jackshafer/zmk-config-biba40/images/Biba40_v2_underside.jpg

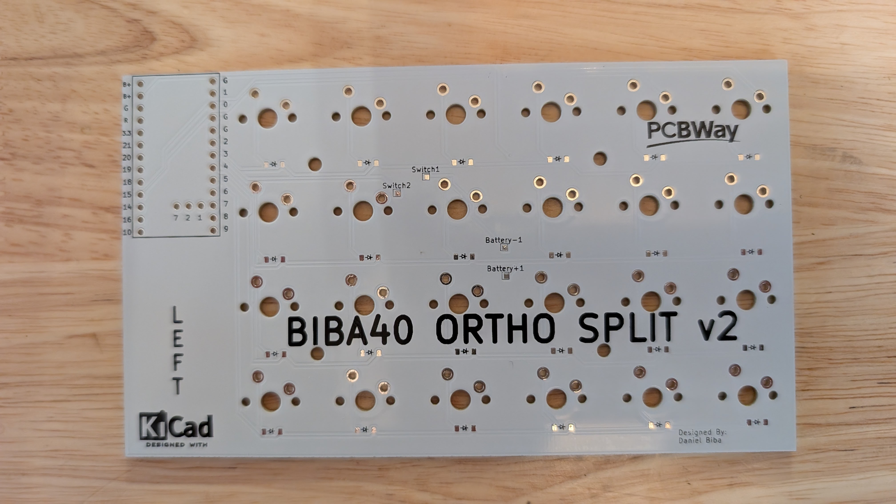
images/Biba40_v2_underside.jpg
