jackshafer/zmk-config-biba40/images/grey_and_purple_keycaps.jpg

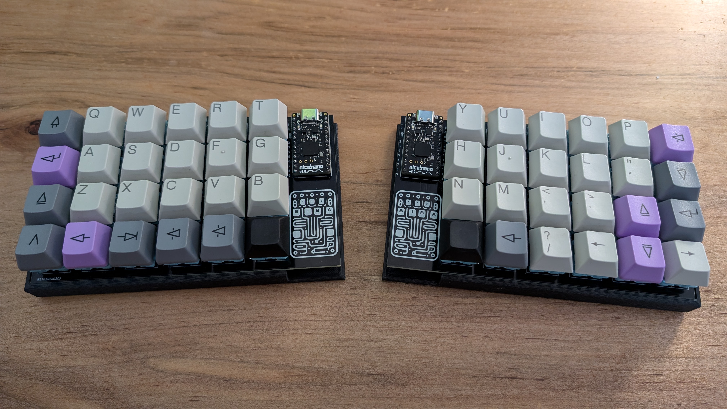
images/grey_and_purple_keycaps.jpg
