jackshafer/zmk-config-biba40/images/nice_nano.jpg

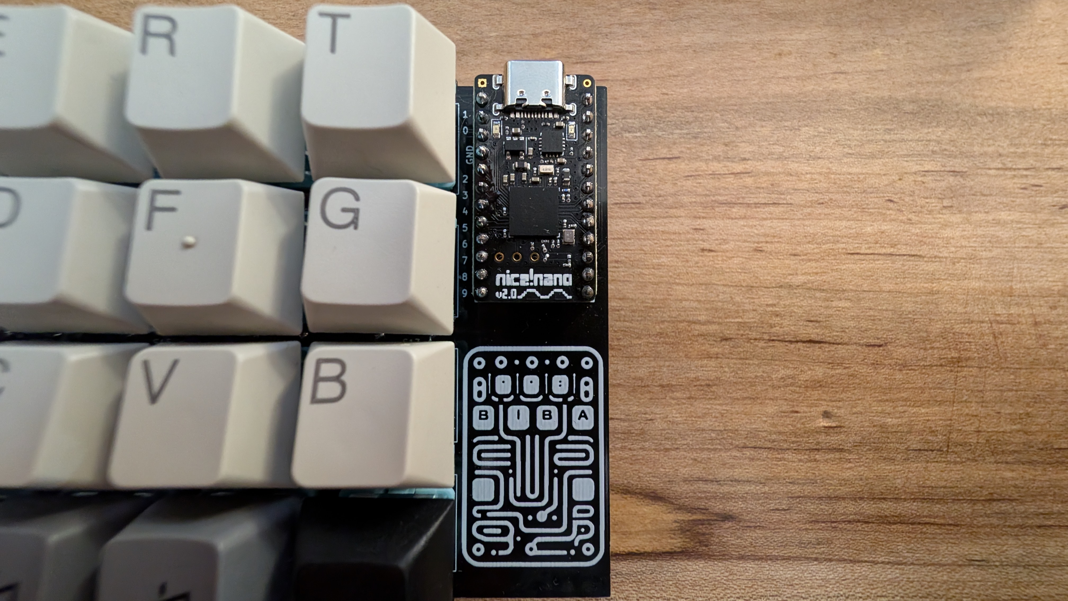
images/nice_nano.jpg
