jackshafer/zmk-config-biba40/images/power_switch.jpg

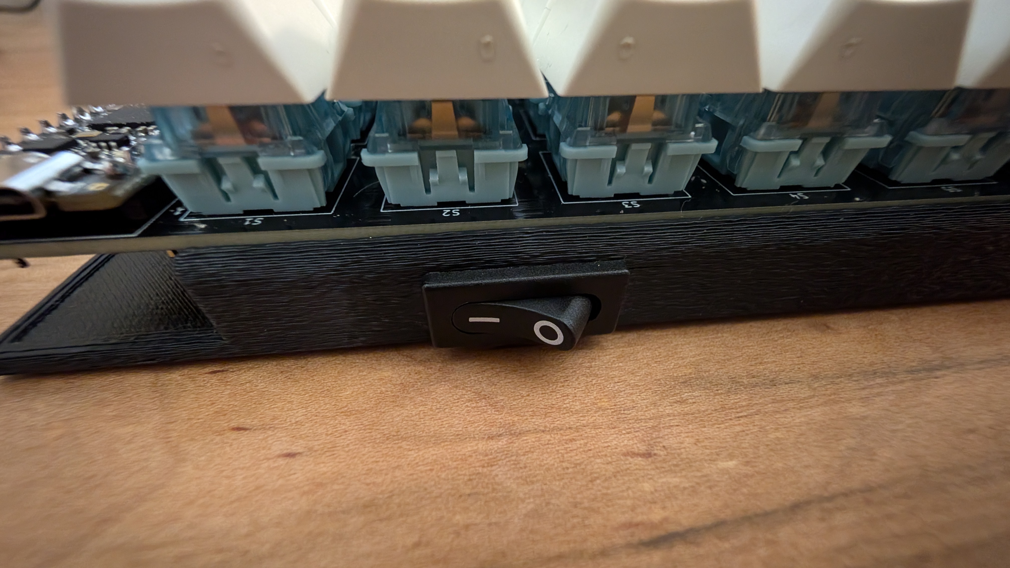
images/power_switch.jpg
