jackshafer/zmk-config-biba40/images/PXL_20250227_141126423.jpg

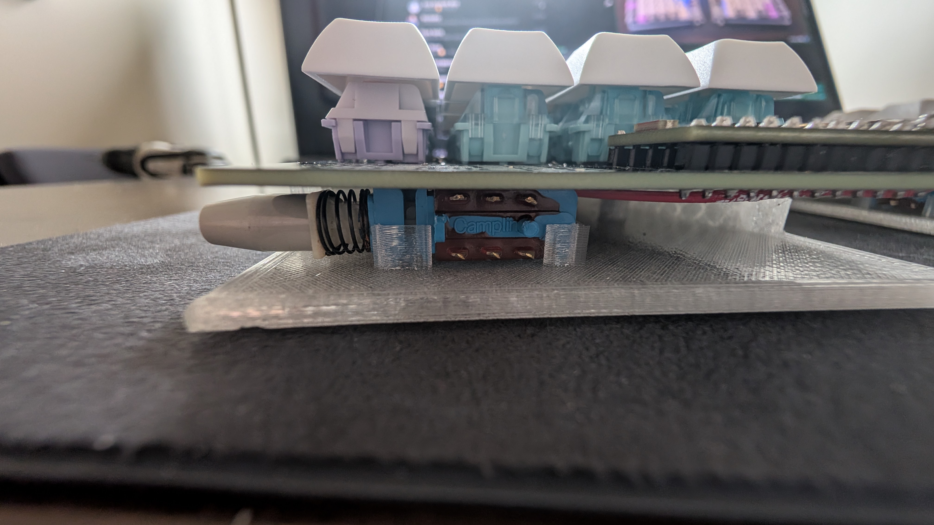
images/PXL_20250227_141126423.jpg
