jackshafer/zmk-config-biba40/images/PXL_20250227_221245341.PORTRAIT.ORIGINAL.jpg

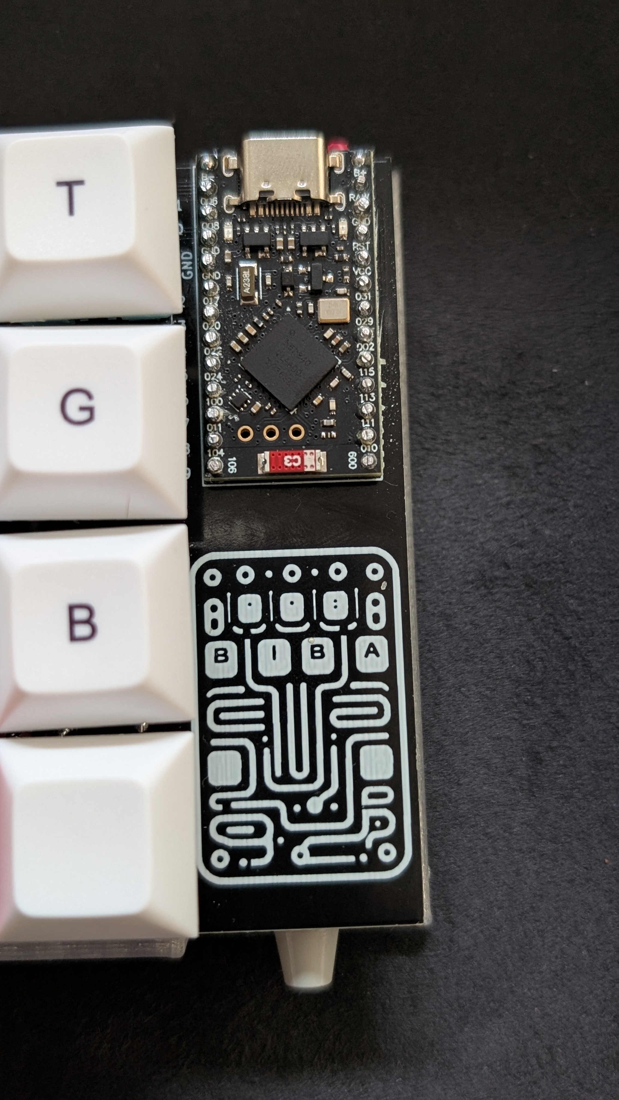
images/PXL_20250227_221245341.PORTRAIT.ORIGINAL.jpg
