jackshafer/zmk-config-biba40/images/right_side.jpg

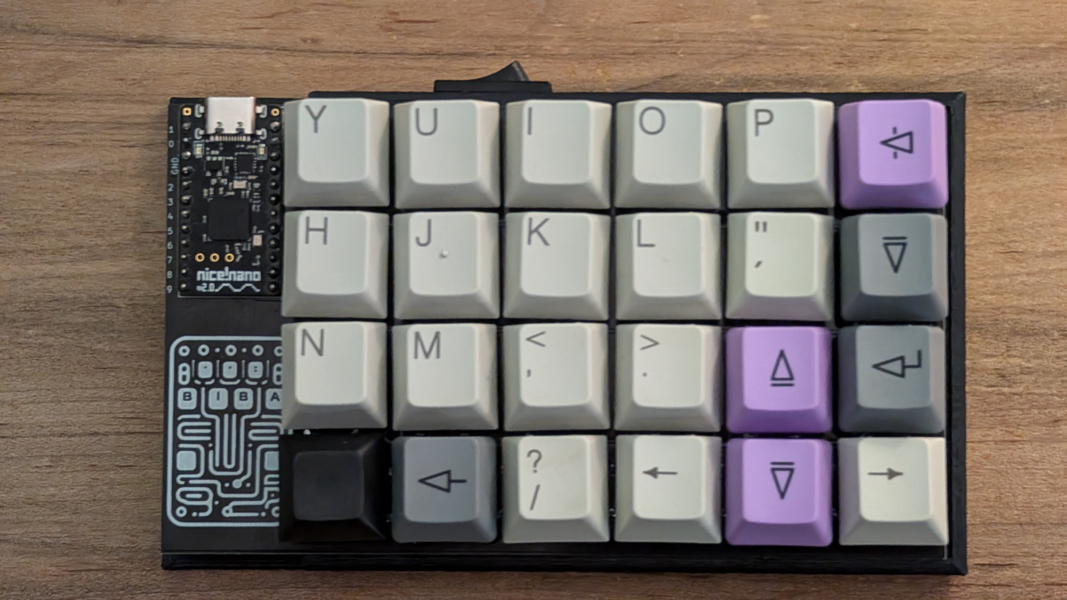
images/right_side.jpg
