jackshafer/zmk-config-biba40/images/Rubber_feet_one.jpg

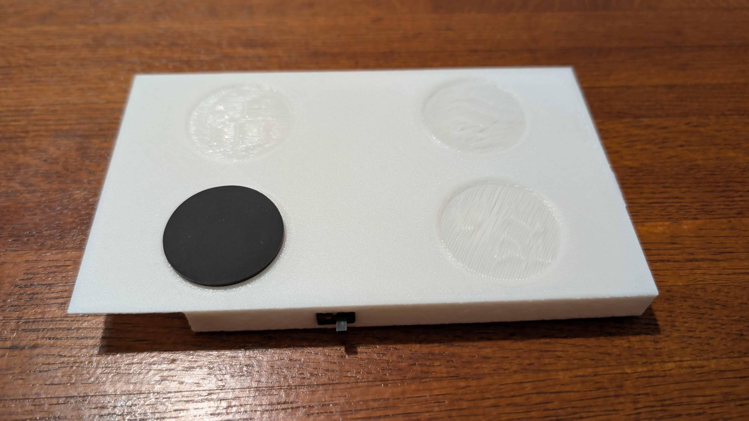
images/Rubber_feet_one.jpg
