jackshafer/zmk-config-biba40/images/top_side.jpg

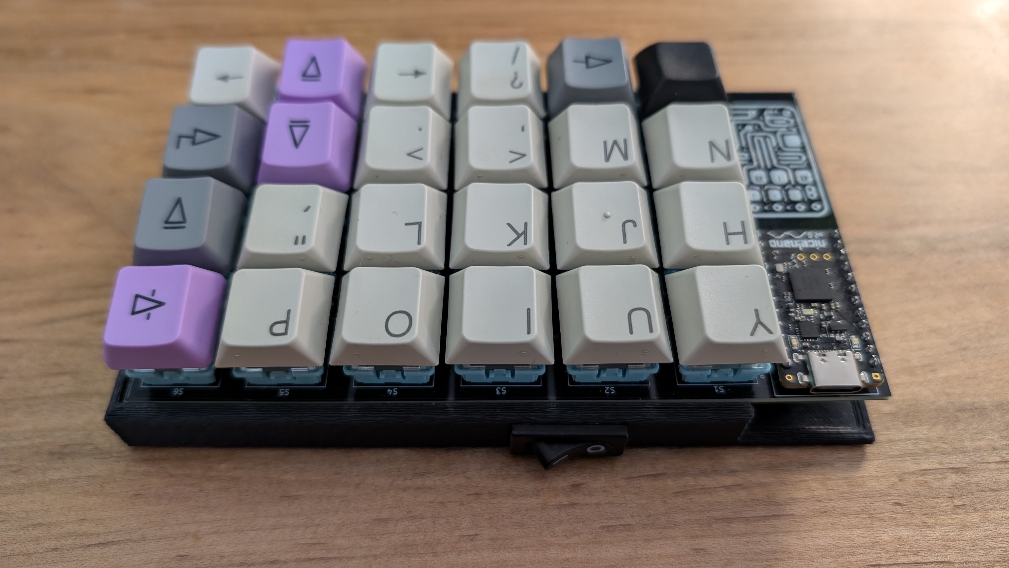
images/top_side.jpg
